GabrieleTrigliaUNIGE/esp32_oscilloscopio/hardware/esp32_oscilloscope.kicad_sch

## KiCad design hardware/esp32_oscilloscope.kicad_sch (2026-03-28)

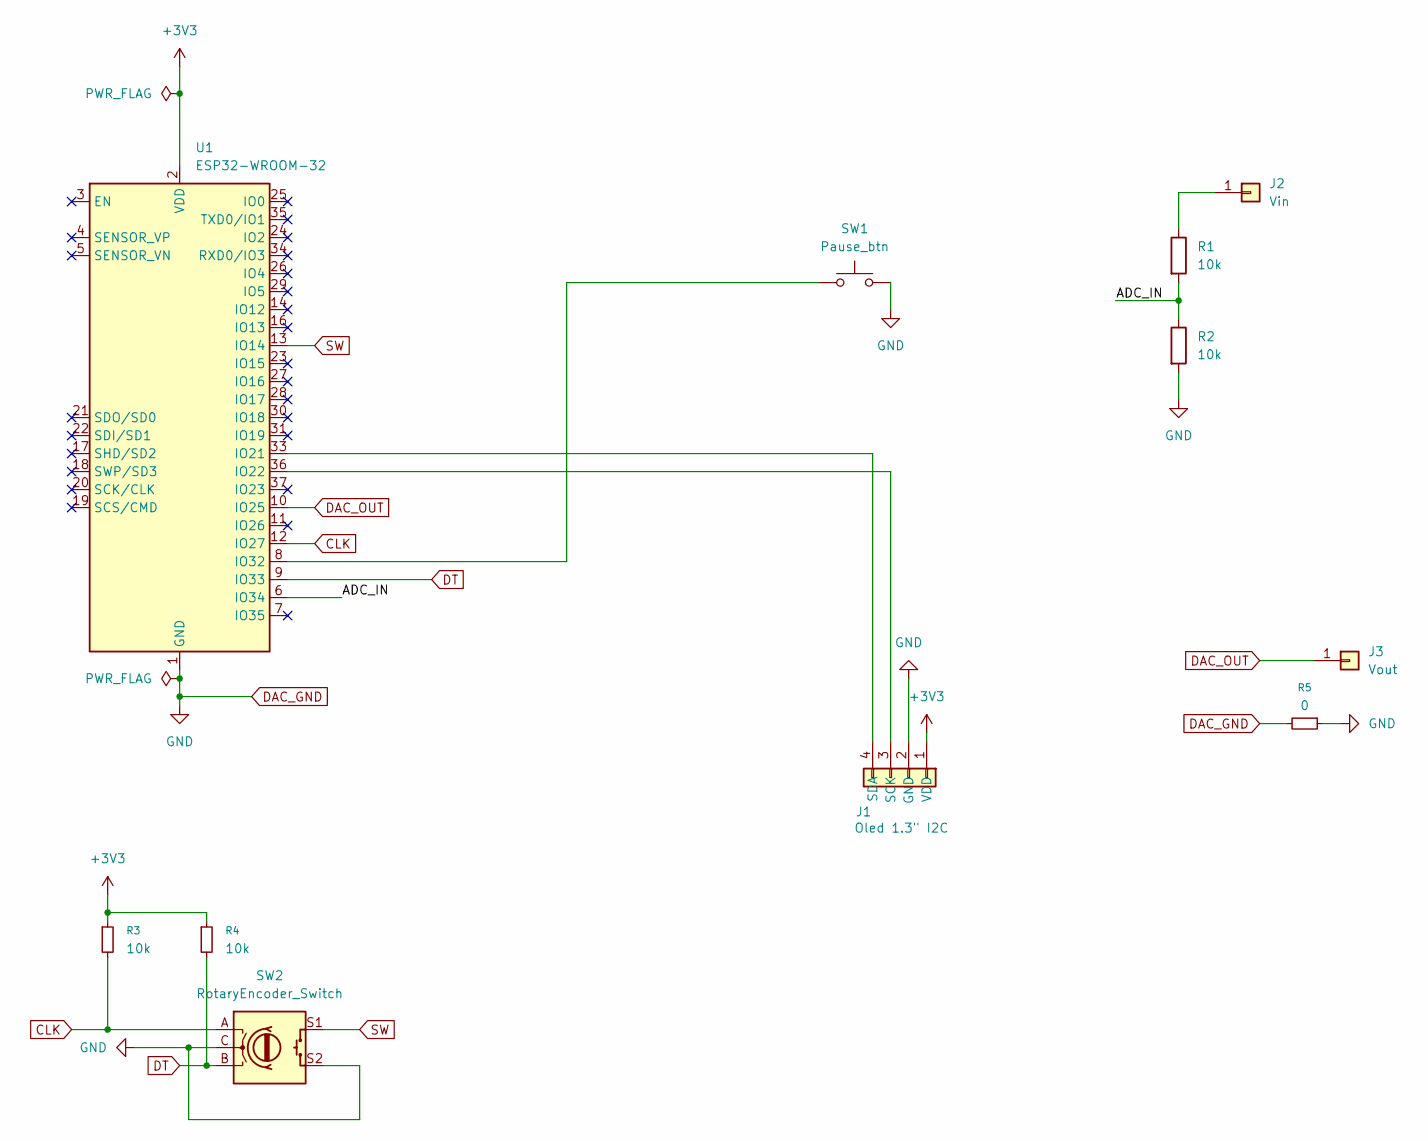
[picture p3: schematic esp32_oscilloscope.kicad_sch]

Parts:
J1: Oled 1.3" I2C
J2: Vin
J3: Vout
R1, R2, R3, R4: 10k
R5: 0
SW1: Pause_btn
SW2: RotaryEncoder_Switch
U1: ESP32-WROOM-32

Connections:
+3V3: J1.1 (VDD), R3.1, R4.1, U1.2 (VDD)
ADC_IN: R1.2, R2.1, U1.6 (IO34)
CLK: R3.2, SW2.A, U1.12 (IO27)
DAC_GND: J1.2 (GND), R2.2, R5.1, R5.2, SW1.2, SW2.C, SW2.S2, U1.1 (GND), U1.15 (GND), U1.38 (GND), U1.39 (GND)
DAC_OUT: J3.1, U1.10 (IO25)
DT: R4.2, SW2.B, U1.9 (IO33)
unnamed: J1.3 (SCK), U1.36 (IO22)
unnamed: J1.4 (SDA), U1.33 (IO21)
unnamed: J2.1, R1.1
unnamed: SW1.1, U1.8 (IO32)
SW: SW2.S1, U1.13 (IO14)
